EMajesty/elecrig/adapters/pedal/eventide/space/README.md

# Eventide Space

Elecrig mount for the Eventide Space.

Mounted device

## Compatibility

- **Device:** Eventide Space
- **Interface:** ER80
- **Rail span:** 2
- **Tested:** Yes

## Hardware

**Device attachment:** Original screws  
**Rubber feet:** Keep

### Additional device hardware

- None

### Rail hardware

- 4 × M5×10 bolts
- 4 × M5 hammer nuts

## Files

- `cad/` — STEP files
- `print/` — ready-to-print 3MF files
- `images/` — reference and installation photos

## Printing

**Material:**
**Supports:**

## Installation

## CAD

https://cad.onshape.com/documents/e6d982047e9a278fe3f14910/w/8a50545e375b66e950502b89/e/abb22506fef7655021bbcef4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

## Notes
