EMajesty/elecrig/adapters/pedal/hammond/125b/README.md

# Hammond 125B

Elecrig mount for the Hammond 125B.

Mounted device

## Compatibility

- **Device:** Hammond 125B
- **Interface:** ER80
- **Rail span:** 2
- **Tested:** Yes

## Hardware

**Device attachment:** Original screws  
**Rubber feet:** Depends on the pedal

### Additional device hardware

- None

### Rail hardware

- 4 × M5×10 bolts
- 4 × M5 hammer nuts

## Files

- `cad/` — STEP files
- `print/` — ready-to-print 3MF files
- `images/` — reference and installation photos

## Printing

**Material:**
**Supports:**

## Installation

## CAD

https://cad.onshape.com/documents/e6d982047e9a278fe3f14910/w/8a50545e375b66e950502b89/e/f160fbc8cfea4b1bf10c5553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

## Notes
