EMajesty/elecrig/adapters/pedal/strymon/timeline/README.md

# Strymon Timeline

Elecrig mount for the Strymon Timeline.

Mounted device

## Compatibility

- **Device:** Strymon Timeline
- **Interface:** ER80
- **Rail span:** 2
- **Tested:** Yes

## Hardware

**Device attachment:** Original screws  
**Rubber feet:** [Keep / Remove / N/A]

### Additional device hardware

- None

### Rail hardware

- 4 × M5×10 bolts
- 4 × M5 hammer nuts

## Files

- `cad/` — STEP files
- `print/` — ready-to-print 3MF files
- `images/` — reference and installation photos

## Printing

**Material:**
**Supports:**

## Installation

## CAD

https://cad.onshape.com/documents/e6d982047e9a278fe3f14910/w/8a50545e375b66e950502b89/e/ed0f745f2ee5de4cc99ad26a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

## Notes
