EMajesty/elecrig/adapters/psu/cioks/crux/README.md

# Cioks Crux

Elecrig mount for the Cioks Crux.

Mounted device

## Compatibility

- **Device:** Cioks Crux
- **Interface:** ER80
- **Rail span:** 2
- **Tested:** Yes

## Hardware

**Device attachment:** Additional screws  
**Rubber feet:** N/A

### Additional device hardware

- 2 × M4×6 countersunk bolts

### Rail hardware

- 2 × M5×10 bolts
- 2 × M5 hammer nuts

## Files

- `cad/` — STEP files
- `print/` — ready-to-print 3MF files
- `images/` — reference and installation photos

## Printing

**Material:**   
**Supports:** 

## Installation

Mounts vertically.

## CAD

https://cad.onshape.com/documents/e6d982047e9a278fe3f14910/w/8a50545e375b66e950502b89/e/50ef58d5d7de5d0ba44d7a87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

## Notes
