EMajesty/elecrig/adapters/psu/cioks/dc7/README.md

# Cioks DC7

Elecrig mount for the Cioks DC7.

Mounted device

## Compatibility

- **Device:** Cioks DC7
- **Interface:** ER80
- **Rail span:** 2
- **Tested:** Yes

## Hardware

**Device attachment:** Additional bolts  
**Rubber feet:** N/A

### Additional device hardware

- 3 × M4×6 bolts

### Rail hardware

- 4 × M5×10 bolts
- 4 × M5 hammer nuts

## Files

- `cad/` — STEP files
- `print/` — ready-to-print 3MF files
- `images/` — reference and installation photos

## Printing

**Material:**  
**Supports:**

## Installation

Mounts horizontally.

## CAD

https://cad.onshape.com/documents/e6d982047e9a278fe3f14910/w/8a50545e375b66e950502b89/e/a6901ba3325bbf756d07ea59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

## Notes
