EMajesty/elecrig/adapters/pedal/neural-dsp/quad-cortex/README.md

# Neural DSP Quad Cortex

Elecrig mount for the Neural DSP Quad Cortex.

Mounted device

## Compatibility

- **Device:** Neural DSP Quad Cortex
- **Interface:** ER80
- **Rail span:** 3
- **Tested:** Yes

## Hardware

**Device attachment:** Original bottom-cover screws  
**Rubber feet:** Remove

### Additional device hardware

- None

### Rail hardware

- 4 × M5×10 bolts
- 4 × M5 hammer nuts

## Files

- `cad/` — STEP files
- `print/` — ready-to-print 3MF files
- `images/` — reference and installation photos

## Printing

**Material:**
**Supports:**

## Installation

## CAD

https://cad.onshape.com/documents/e6d982047e9a278fe3f14910/w/8a50545e375b66e950502b89/e/339f10370a98cb644ed4a976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

## Notes
