EMajesty/elecrig/reference-builds/big - right bottom.3mf

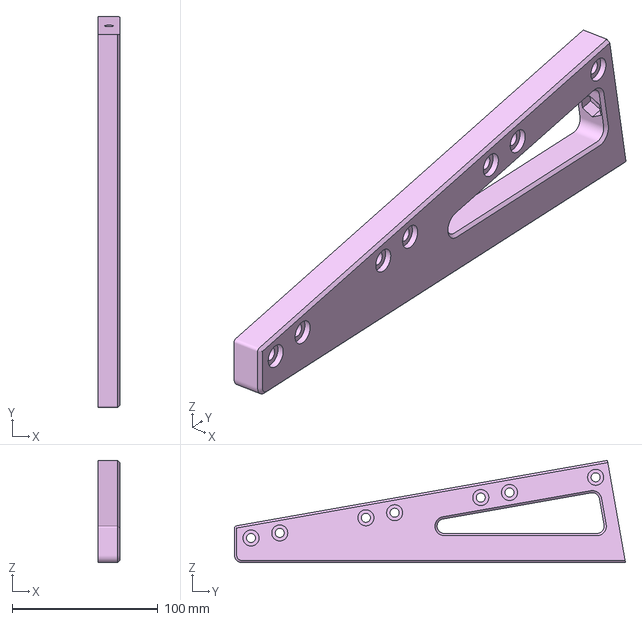
[picture p15: CAD file, 2026-09-06]
reference-builds/big - right bottom.3mf
15.0 x 268.2 x 70.1 mm
