EMajesty/elecrig/adapters/pedal/digitech/whammy-v/print/Digitech Whammy V - top-right.3mf

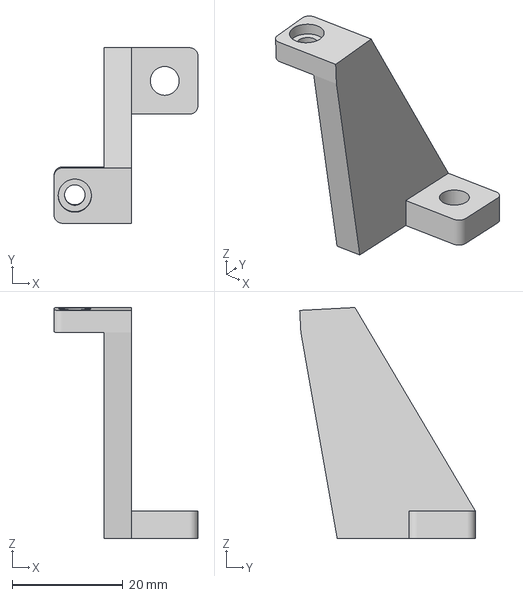
[picture p16: CAD file, 2026-09-04]
adapters/pedal/digitech/whammy-v/print/Digitech Whammy V - top-right.3mf
26.0 x 31.7 x 41.7 mm
