EMajesty/elecrig/reference-builds/big - left top.3mf

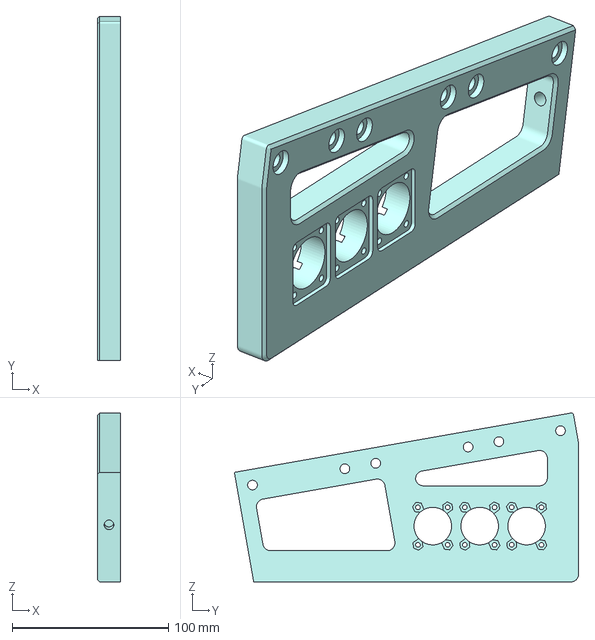
[picture p17: CAD file, 2026-09-06]
reference-builds/big - left top.3mf
15.0 x 220.1 x 108.1 mm
