EMajesty/elecrig/adapters/pedal/digitech/whammy-v/print/Digitech Whammy V - top-left.3mf

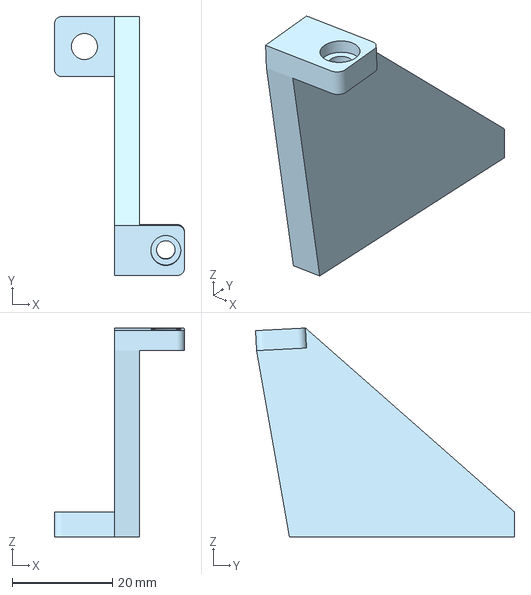
[picture p18: CAD file, 2026-09-04]
adapters/pedal/digitech/whammy-v/print/Digitech Whammy V - top-left.3mf
26.0 x 51.7 x 41.7 mm
