EMajesty/elecrig/adapters/pedal/digitech/whammy-v/print/Digitech Whammy V - bottom-left.3mf

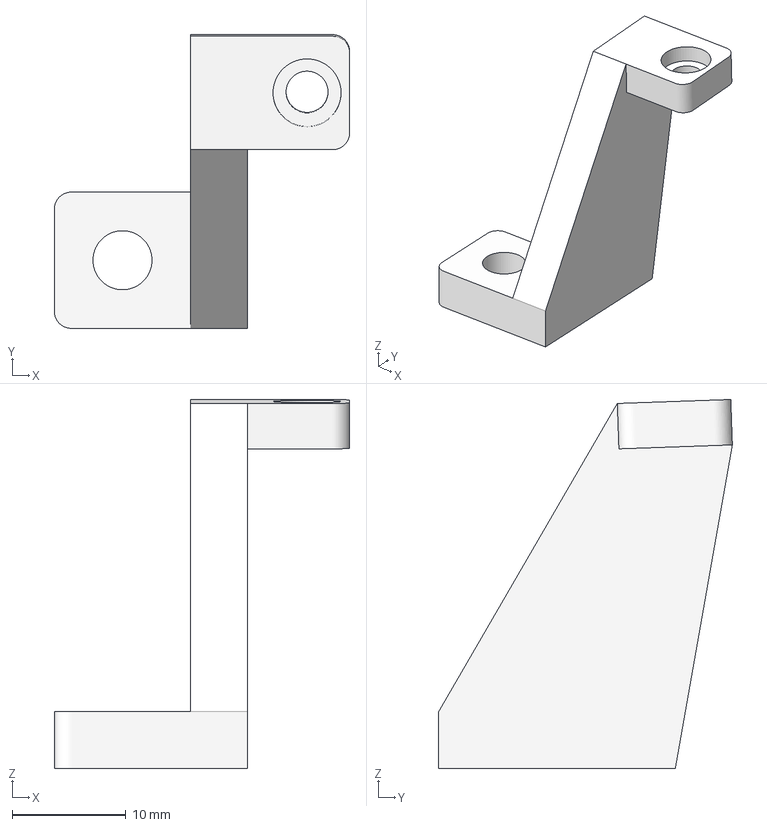
[picture p19: CAD file, 2026-09-04]
adapters/pedal/digitech/whammy-v/print/Digitech Whammy V - bottom-left.3mf
26.0 x 25.9 x 32.5 mm
